adams-liu/SmartMirrorG23/docs/_static/images/app_based_pairing_screenshot_5.png

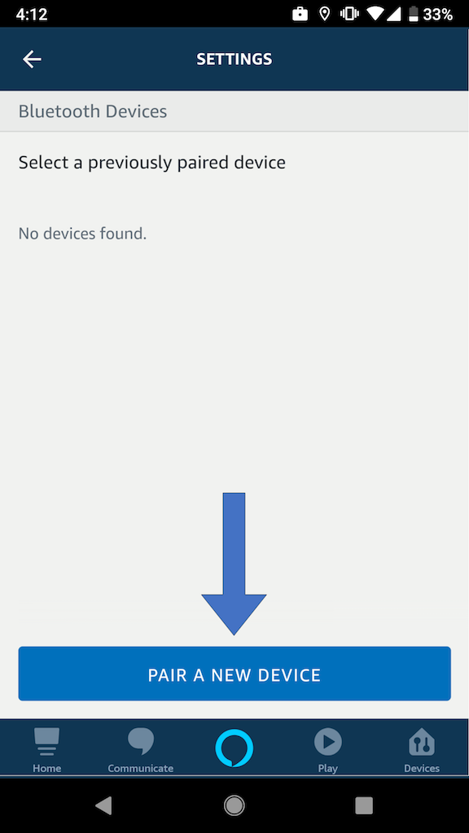
docs/_static/images/app_based_pairing_screenshot_5.png
