adams-liu/SmartMirrorG23/docs/_static/images/button_pinout.png

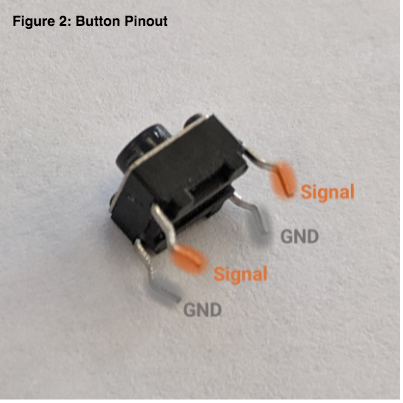
docs/_static/images/button_pinout.png
