adams-liu/SmartMirrorG23/docs/_static/images/color_cycler_gadget.jpg

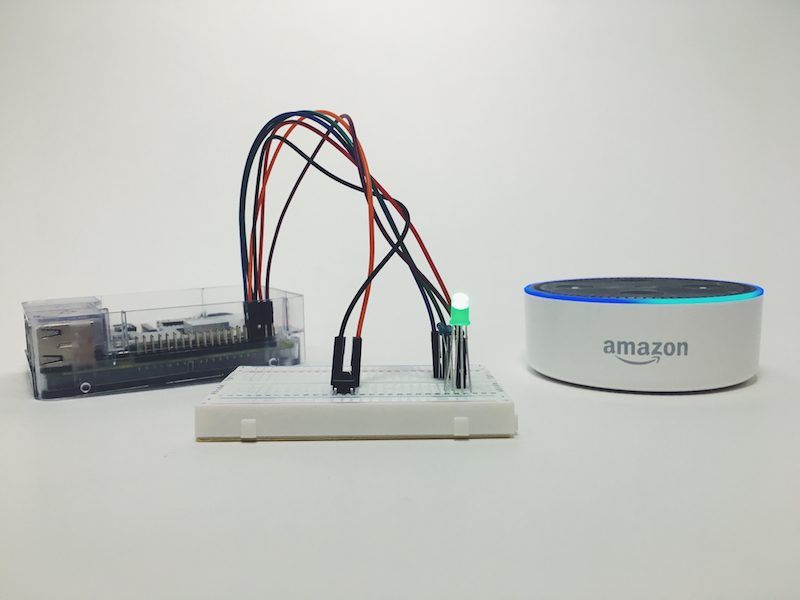
docs/_static/images/color_cycler_gadget.jpg
