adams-liu/SmartMirrorG23/docs/_static/images/colorcycler_skill_creation_screenshot_15.png

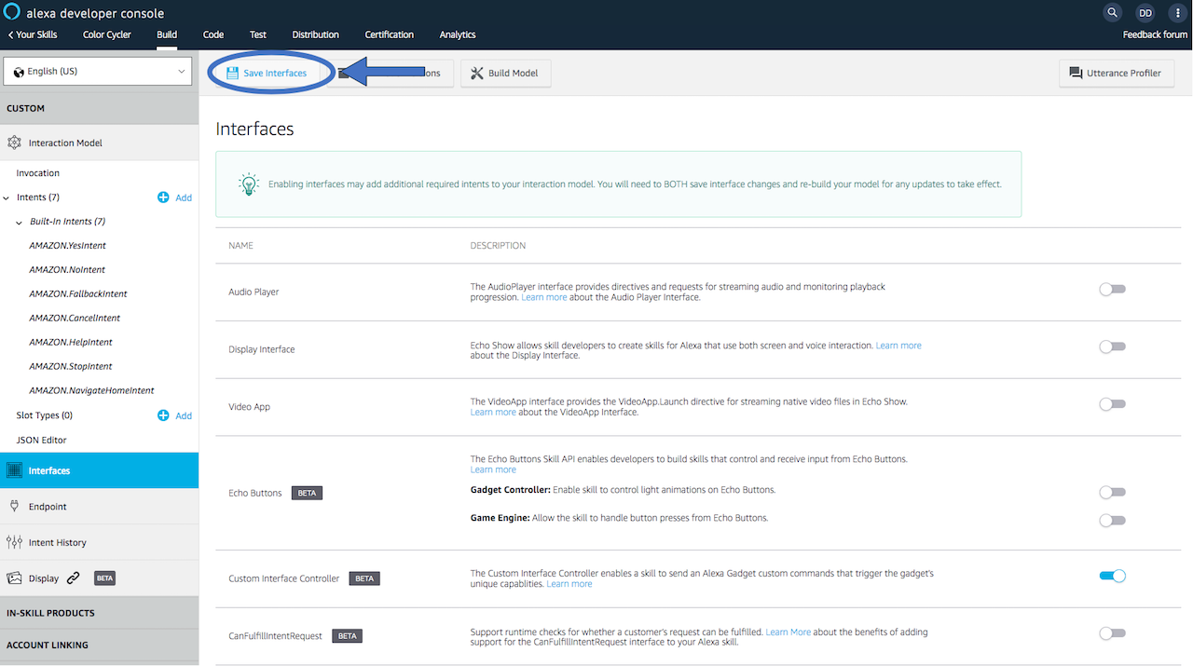
docs/_static/images/colorcycler_skill_creation_screenshot_15.png
