adams-liu/SmartMirrorG23/docs/_static/images/colorcycler_skill_lambda_screenshot_4.png

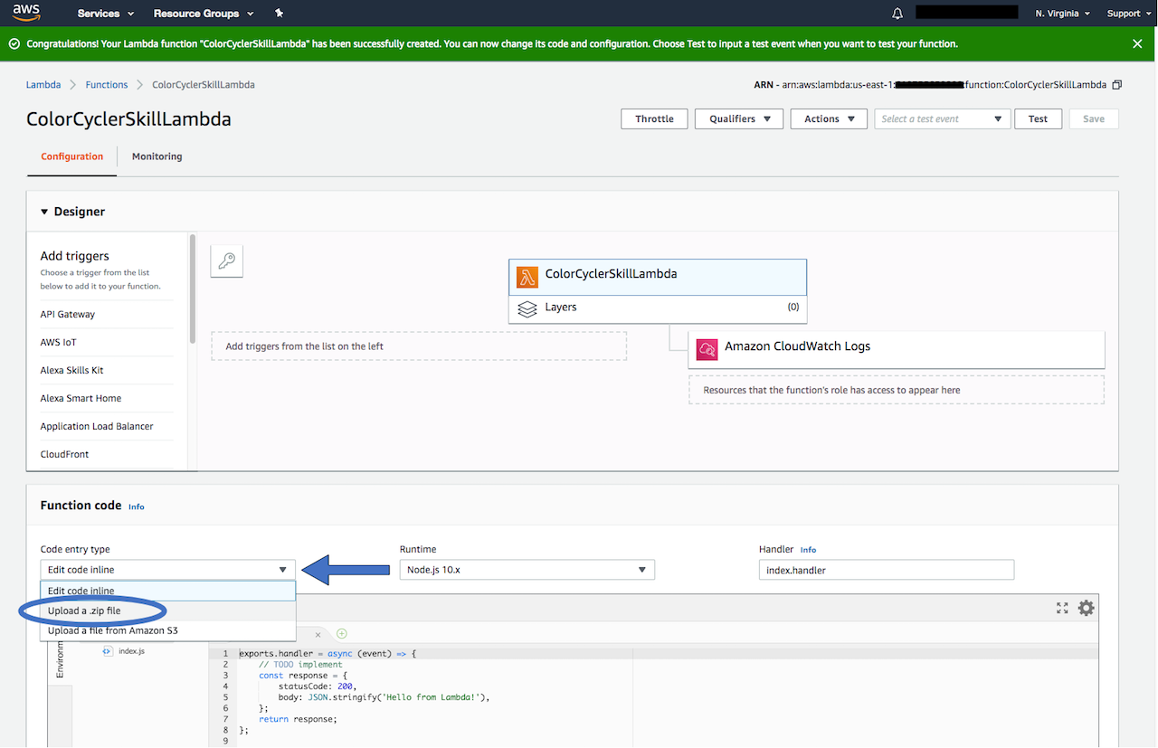
docs/_static/images/colorcycler_skill_lambda_screenshot_4.png
