adams-liu/SmartMirrorG23/docs/_static/images/colorcycler_skill_lambda_screenshot_5.png

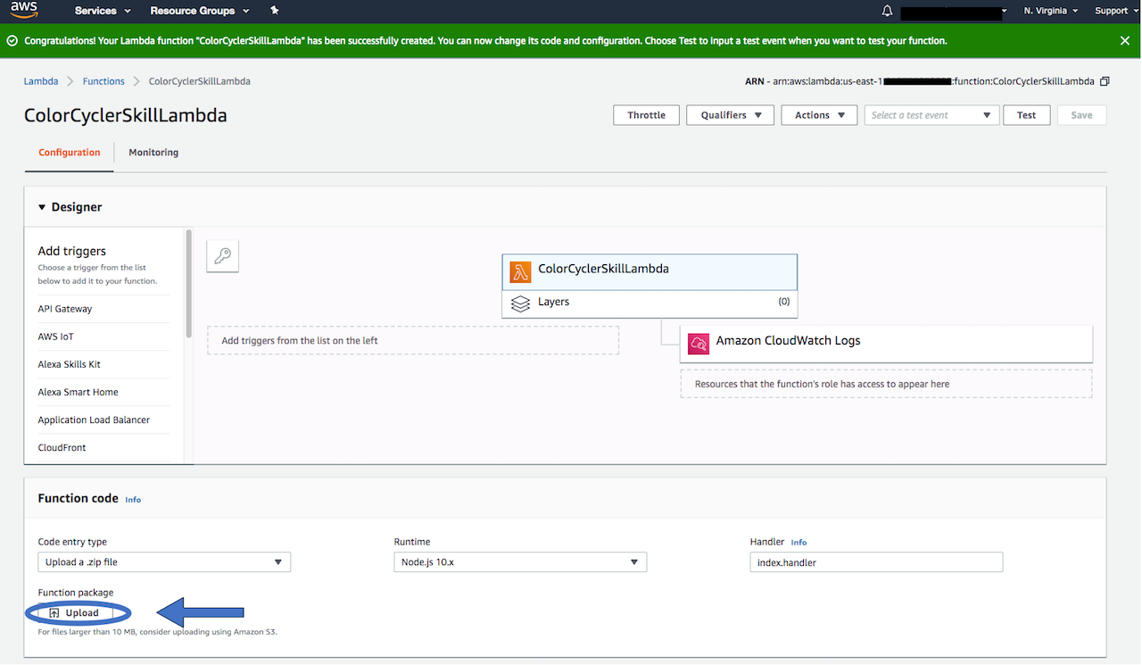
docs/_static/images/colorcycler_skill_lambda_screenshot_5.png
