adams-liu/SmartMirrorG23/docs/_static/images/led_to_rpi.png

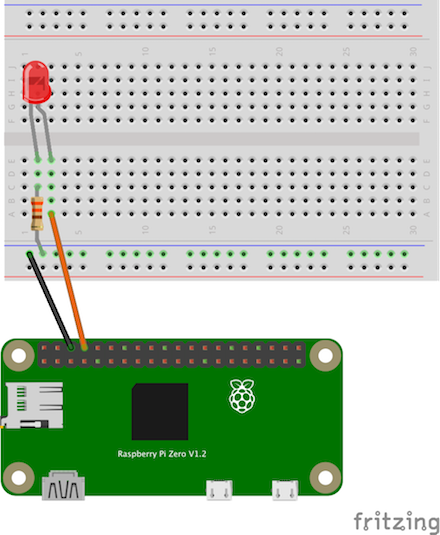
docs/_static/images/led_to_rpi.png
