adams-liu/SmartMirrorG23/docs/_static/images/notification_flag_template.png

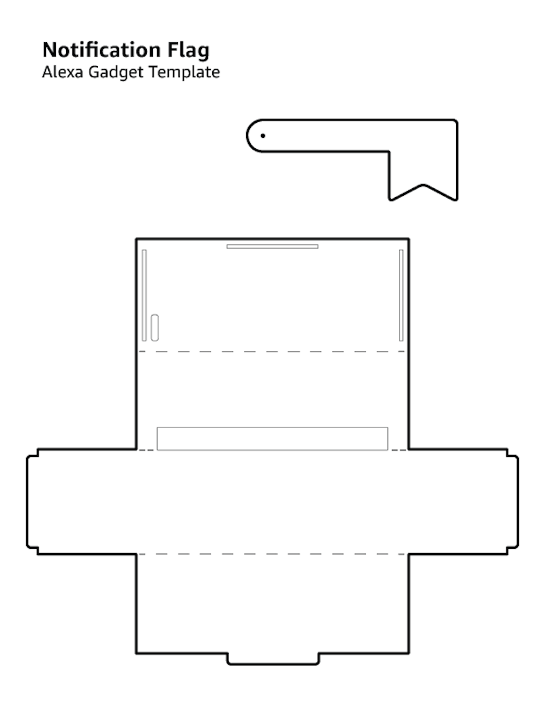
docs/_static/images/notification_flag_template.png
