adams-liu/SmartMirrorG23/docs/_static/images/notification_gadget.png

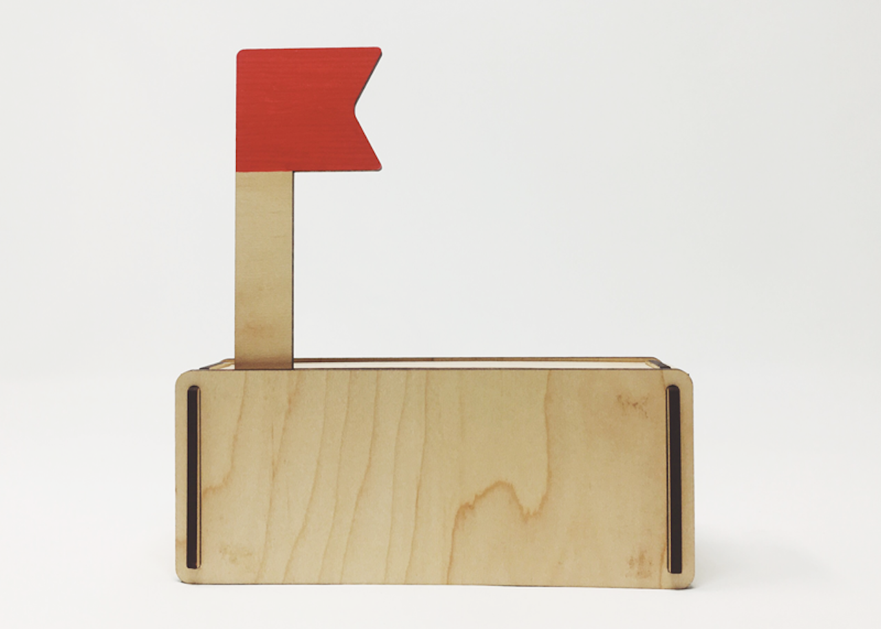
docs/_static/images/notification_gadget.png
