adams-liu/SmartMirrorG23/docs/_static/images/pi_cli_screenshot_0.png

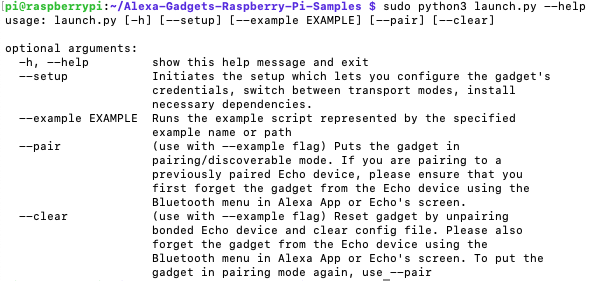
docs/_static/images/pi_cli_screenshot_0.png
