adams-liu/SmartMirrorG23/docs/_static/images/pi_cli_screenshot_7.png

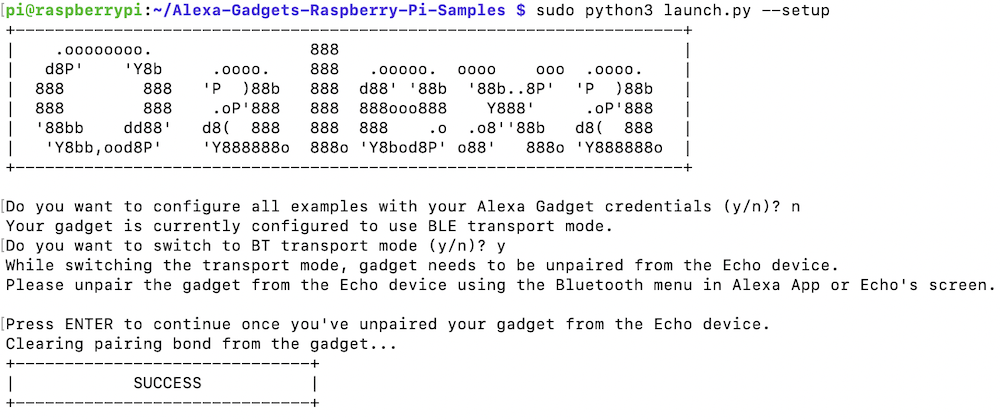
docs/_static/images/pi_cli_screenshot_7.png
