adams-liu/SmartMirrorG23/docs/_static/images/pi_desktop_disable_bt_menu.png

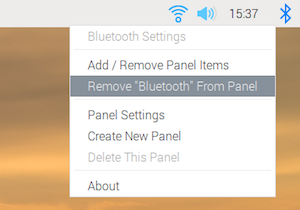
docs/_static/images/pi_desktop_disable_bt_menu.png
