adams-liu/SmartMirrorG23/docs/_static/images/pi_desktop_error_popup.png

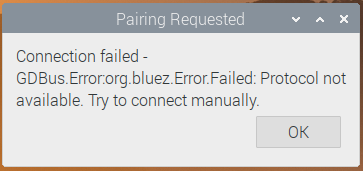
docs/_static/images/pi_desktop_error_popup.png
