adams-liu/SmartMirrorG23/docs/_static/images/pi_led_hardware.png

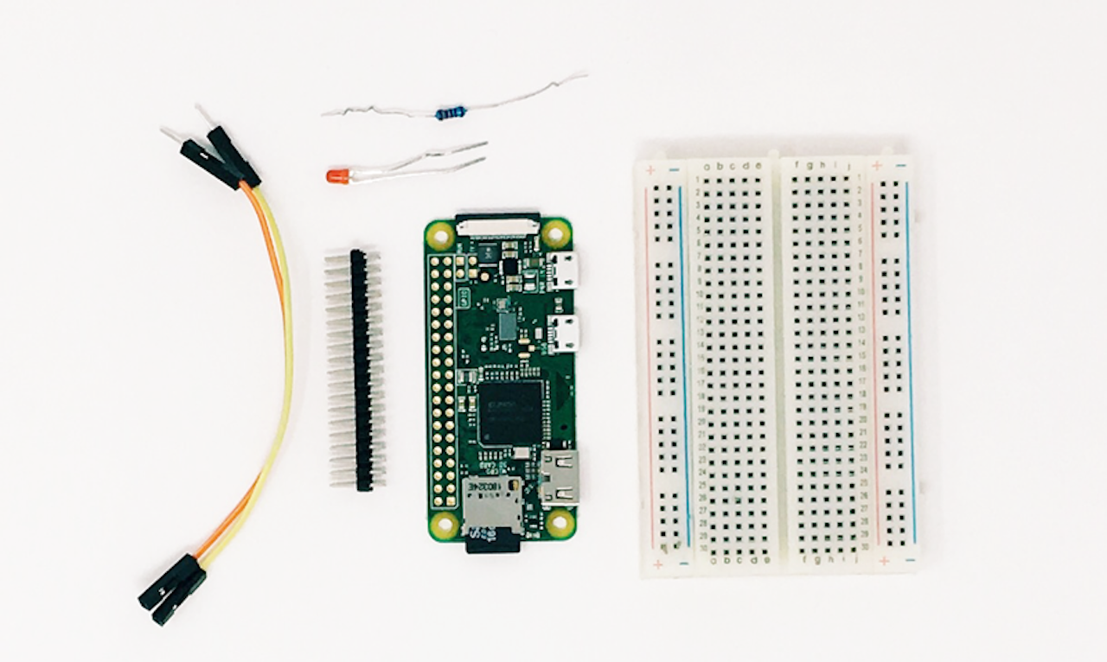
docs/_static/images/pi_led_hardware.png
