adams-liu/SmartMirrorG23/docs/_static/images/pi_servo_hardware.png

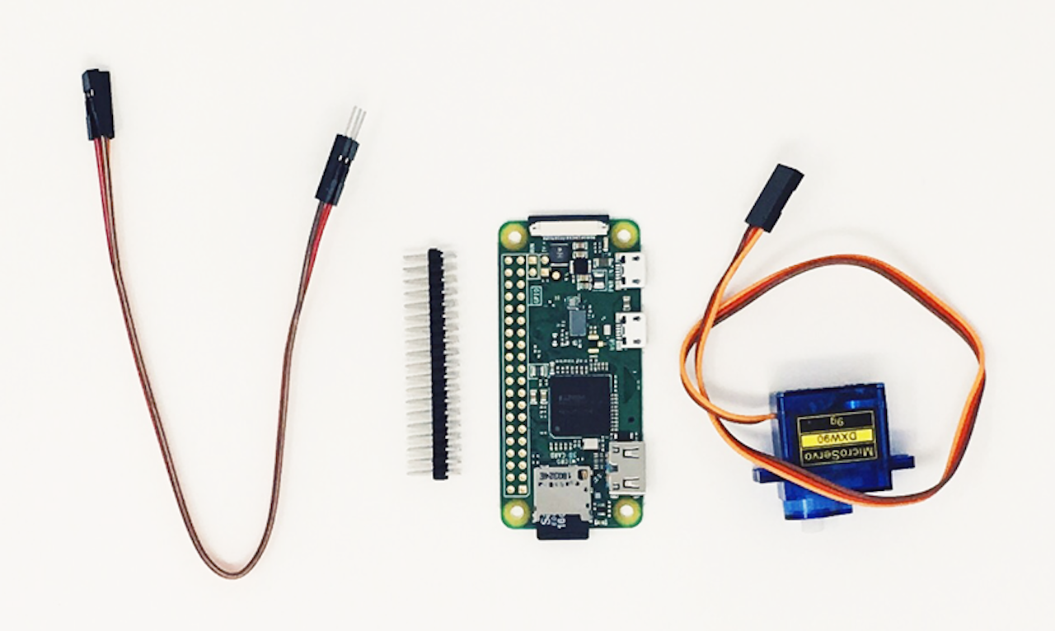
docs/_static/images/pi_servo_hardware.png
