adams-liu/SmartMirrorG23/docs/_static/images/register_gadget_screenshot_1.png

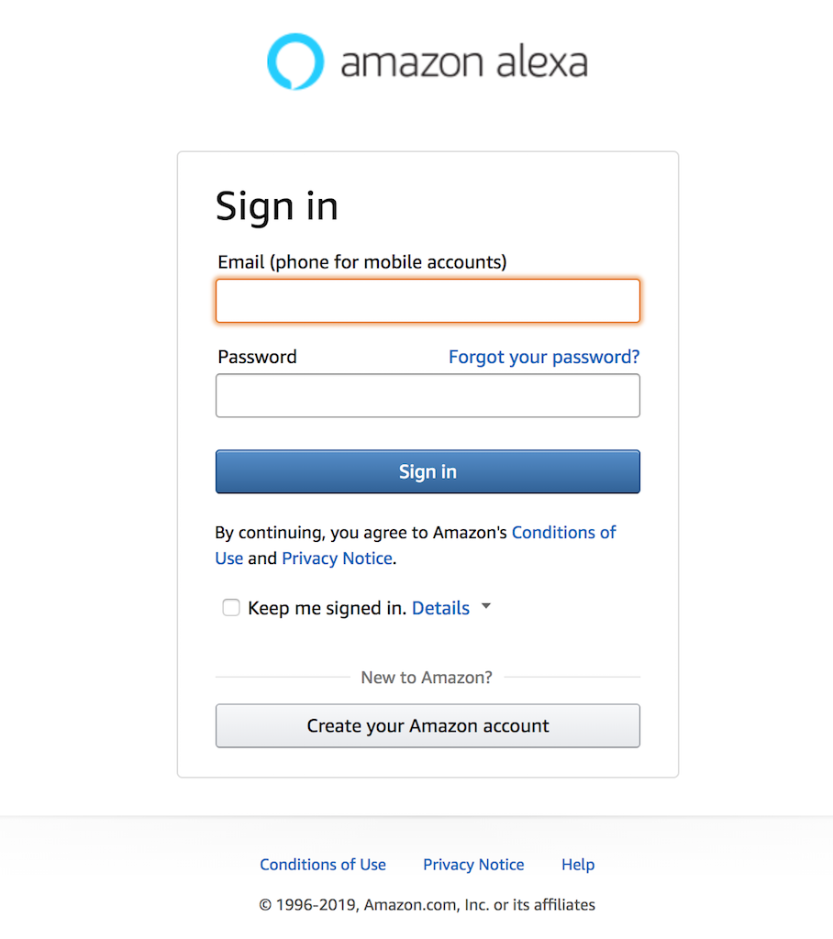
docs/_static/images/register_gadget_screenshot_1.png
