adams-liu/SmartMirrorG23/docs/_static/images/register_gadget_screenshot_4.png

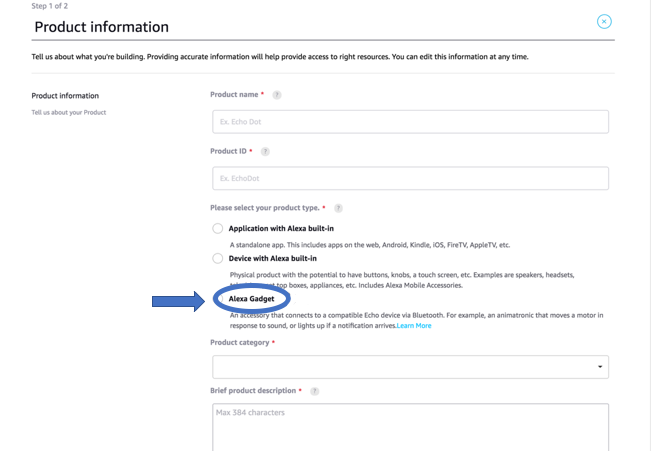
docs/_static/images/register_gadget_screenshot_4.png
