adams-liu/SmartMirrorG23/docs/_static/images/rgb_led_pinout.png

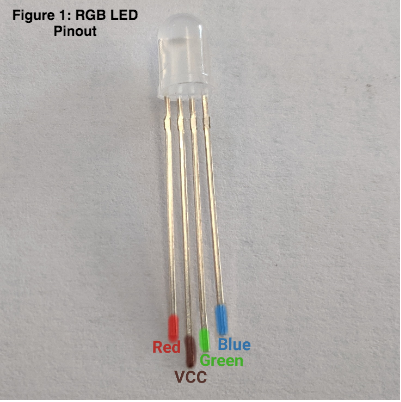
docs/_static/images/rgb_led_pinout.png
