adams-liu/SmartMirrorG23/docs/_static/images/screen_based_pairing_screenshot_2.png

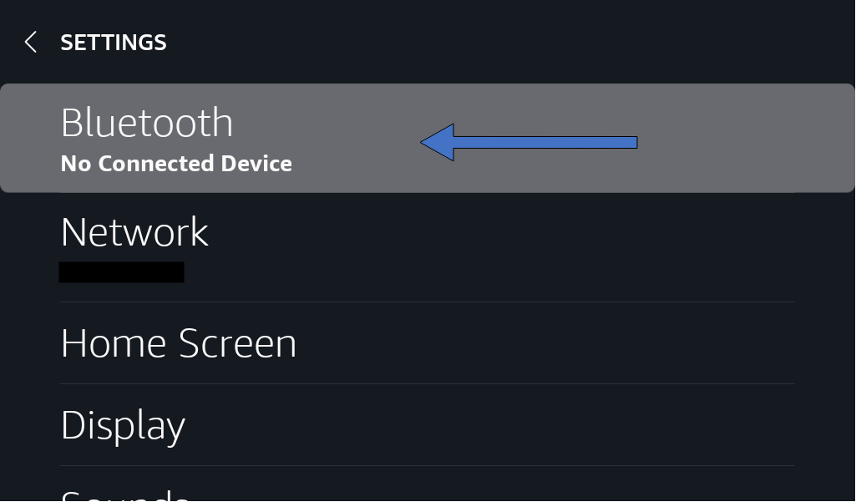
docs/_static/images/screen_based_pairing_screenshot_2.png
