adams-liu/SmartMirrorG23/docs/_static/images/servo_to_rpi.png

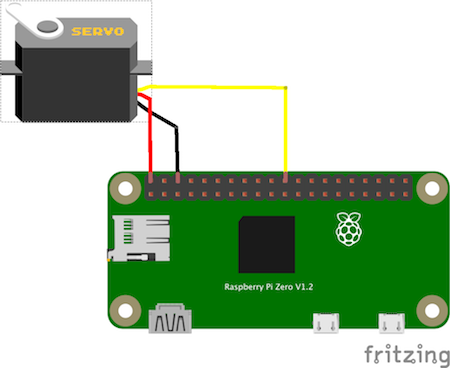
docs/_static/images/servo_to_rpi.png
