adams-liu/SmartMirrorG23/docs/_static/images/timer_gadget.png

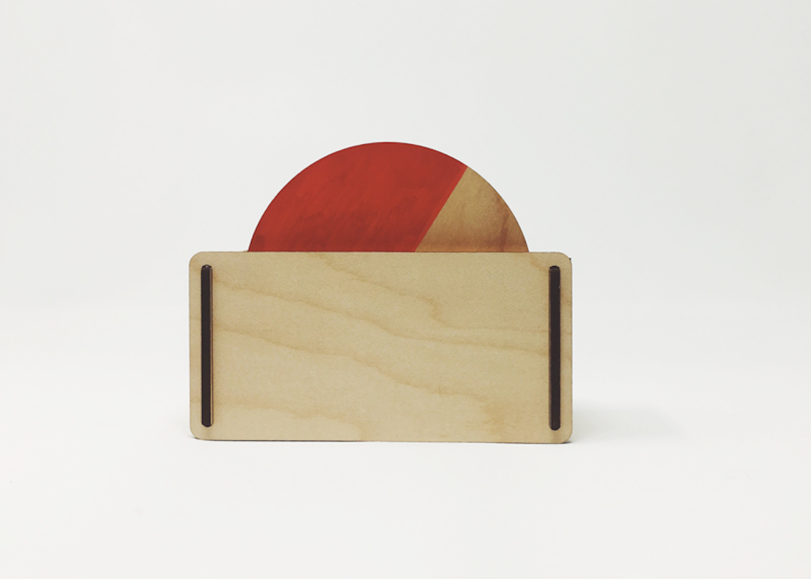
docs/_static/images/timer_gadget.png
