adams-liu/SmartMirrorG23/docs/_static/images/timer_template.png

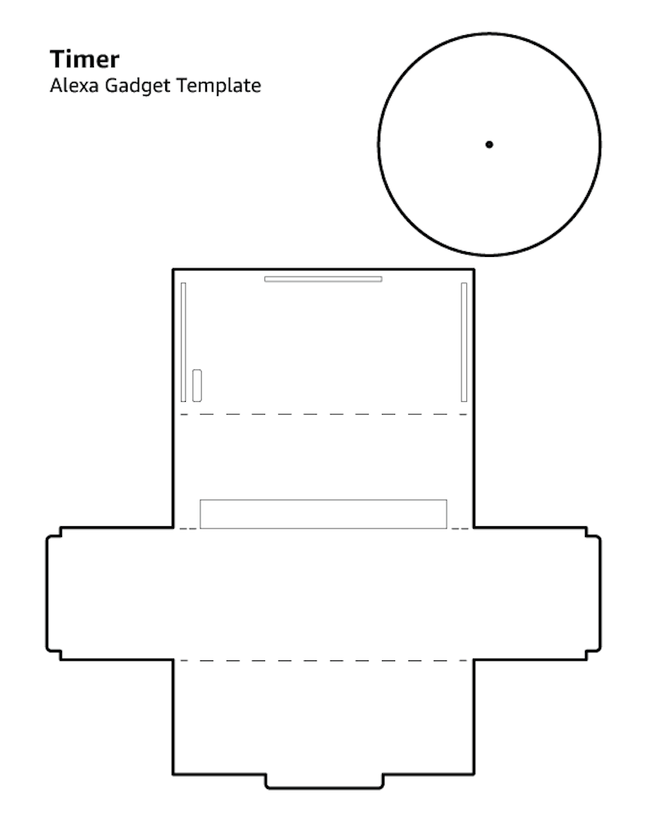
docs/_static/images/timer_template.png
