adams-liu/SmartMirrorG23/docs/source/_static/images/app_based_unpairing_screenshot_3.png

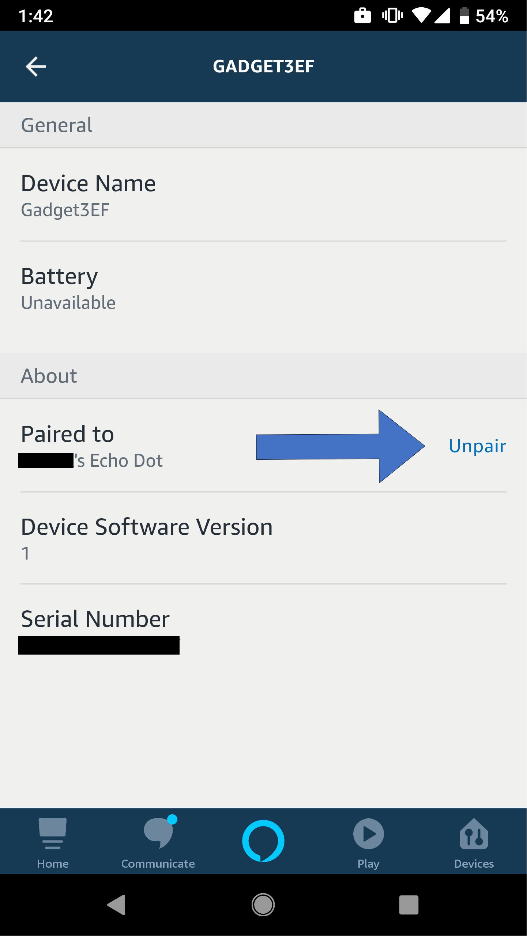
docs/source/_static/images/app_based_unpairing_screenshot_3.png
