adams-liu/SmartMirrorG23/docs/source/_static/images/color_cycler_gadget.png

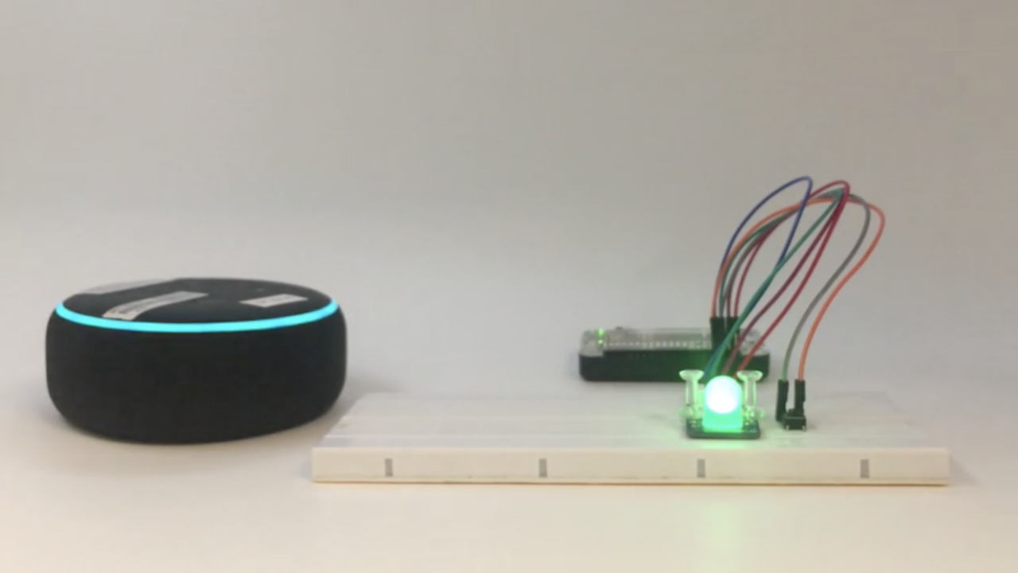
docs/source/_static/images/color_cycler_gadget.png
