adams-liu/SmartMirrorG23/docs/source/_static/images/status_gauge_gadget.png

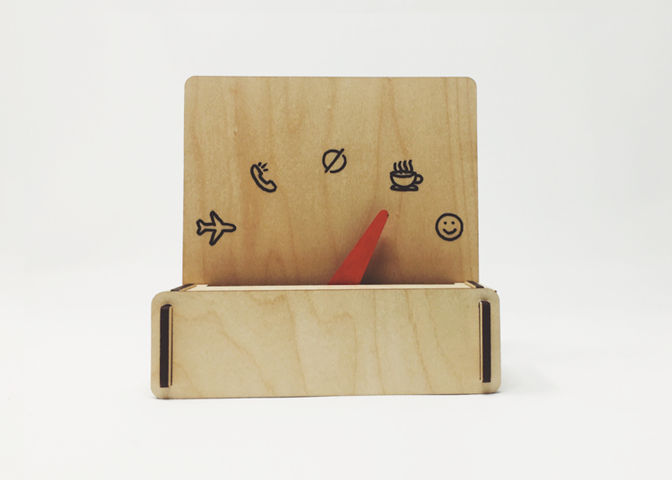
docs/source/_static/images/status_gauge_gadget.png
