adams-liu/SmartMirrorG23/Fullstack/Capture.PNG

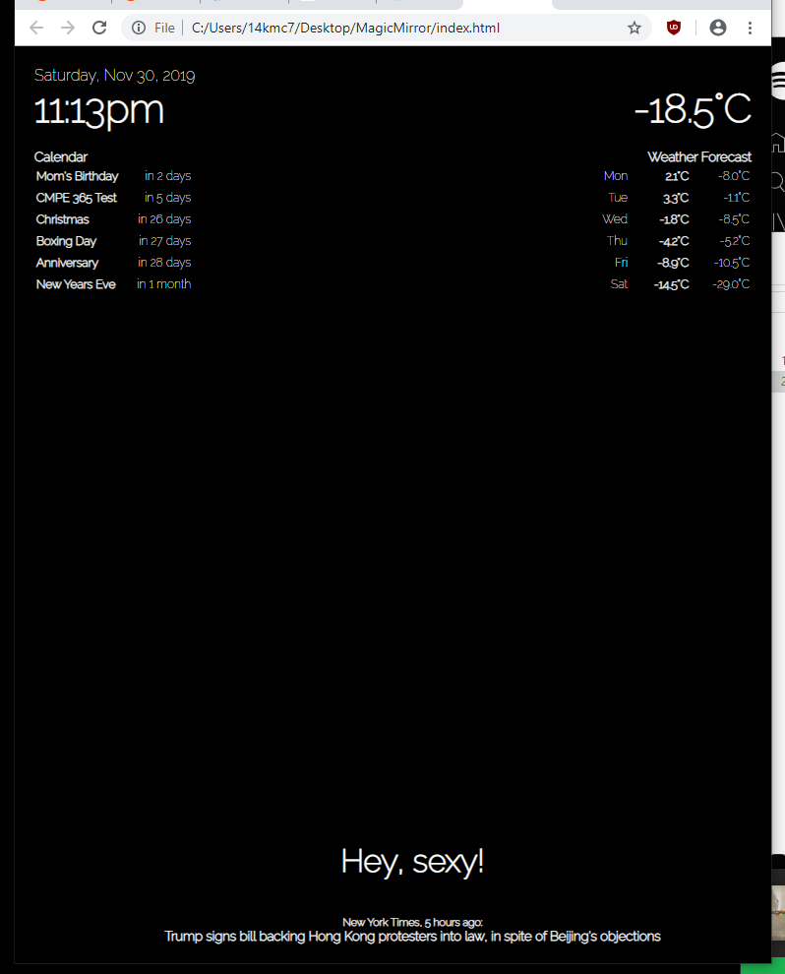
Fullstack/Capture.PNG
