adams-liu/SmartMirrorG23/Hardware/backview.png

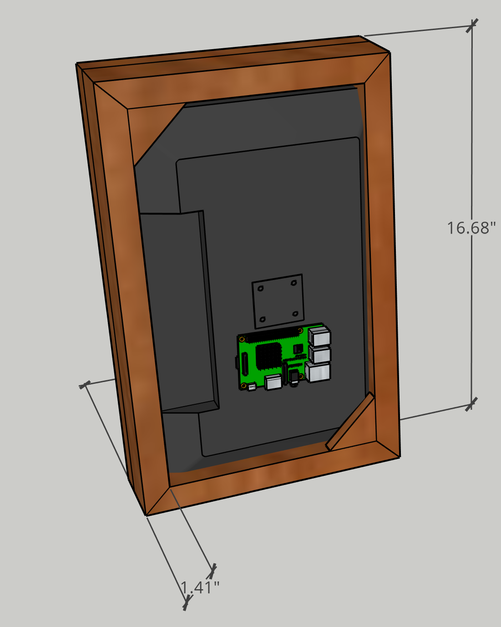
Hardware/backview.png
