adams-liu/SmartMirrorG23/Hardware/frontview.png

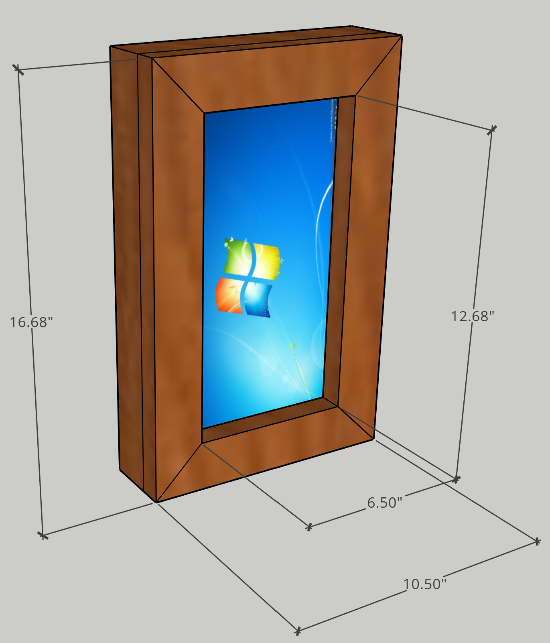
Hardware/frontview.png
