adams-liu/SmartMirrorG23/Hardware/monitorspec.png

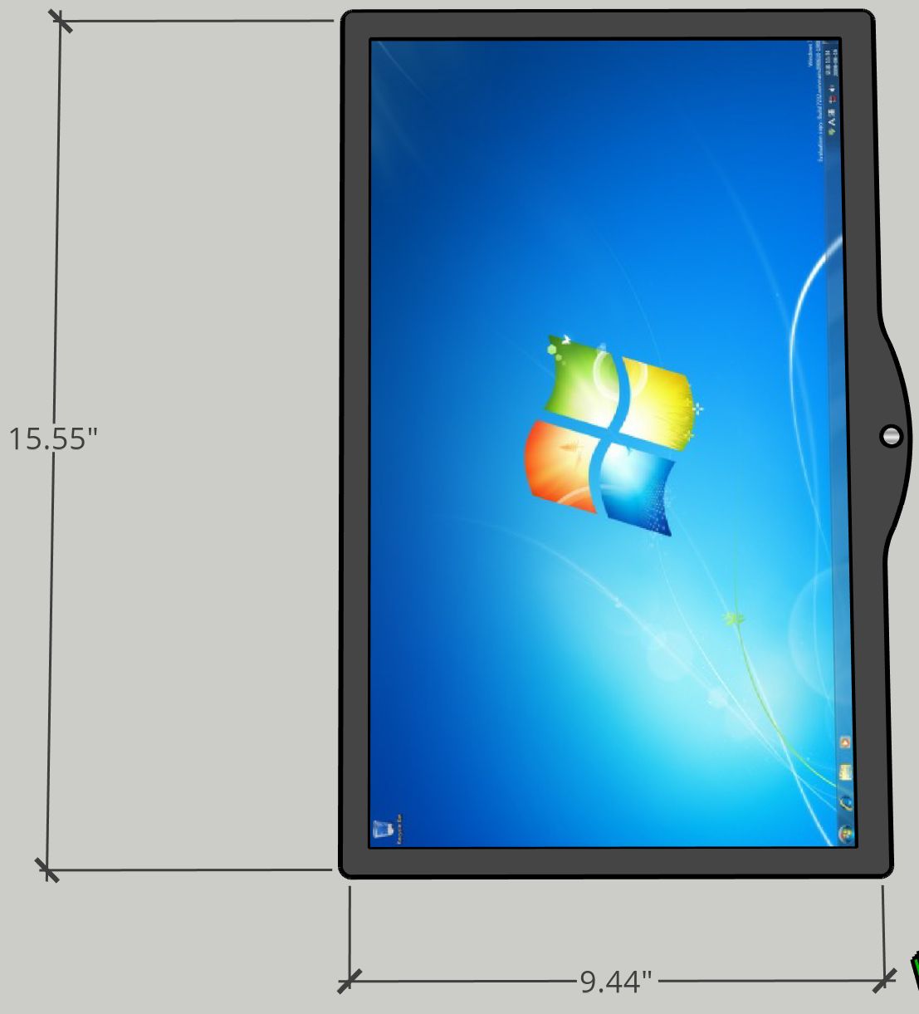
Hardware/monitorspec.png
