adams-liu/SmartMirrorG23/docs/_static/images/color_cycler_components.png

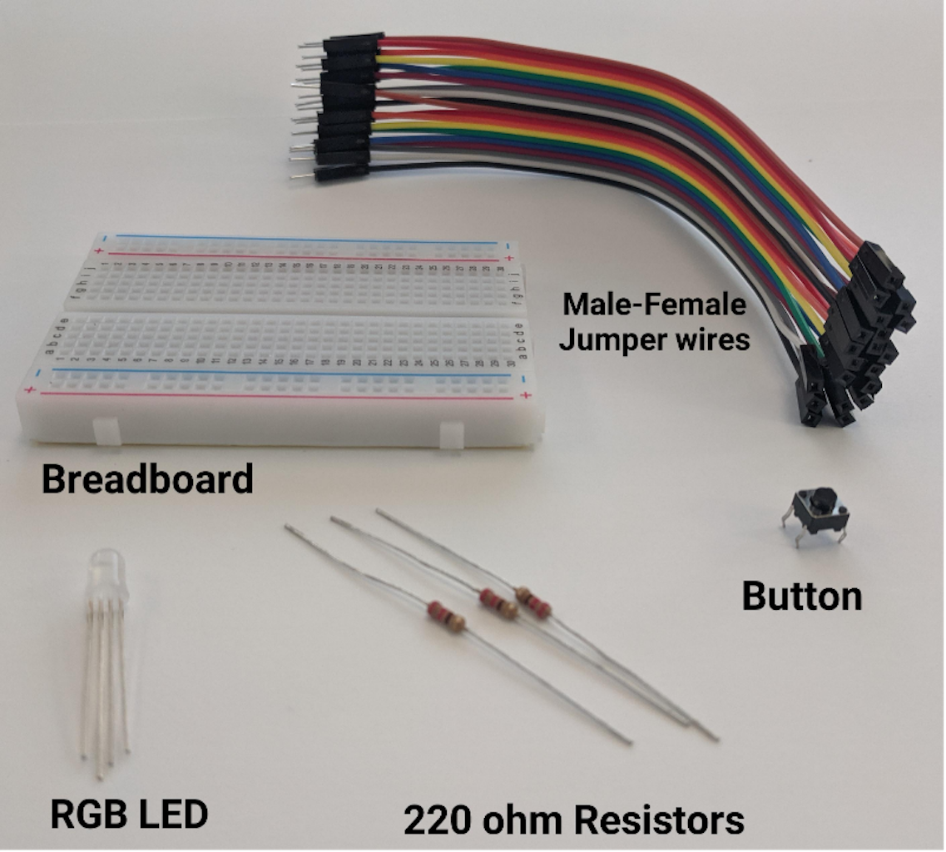
docs/_static/images/color_cycler_components.png
