adams-liu/SmartMirrorG23/docs/build/_static/images/troubleshooting_screenshot_1.png

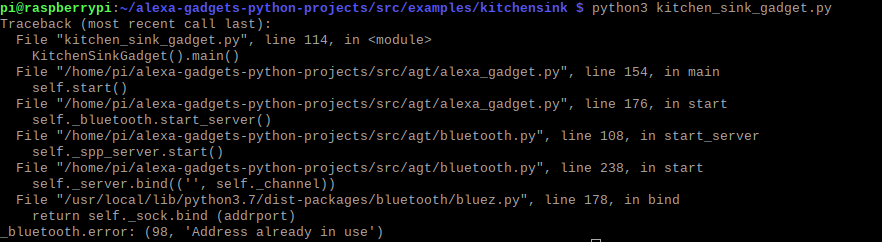
docs/build/_static/images/troubleshooting_screenshot_1.png
